laplacier/PCB-Business-Card-v2/KiCAD Files/PCB_Business_Card_v2.kicad_sch

## KiCad design KiCAD Files/PCB_Business_Card_v2.kicad_sch (2024-06-15)

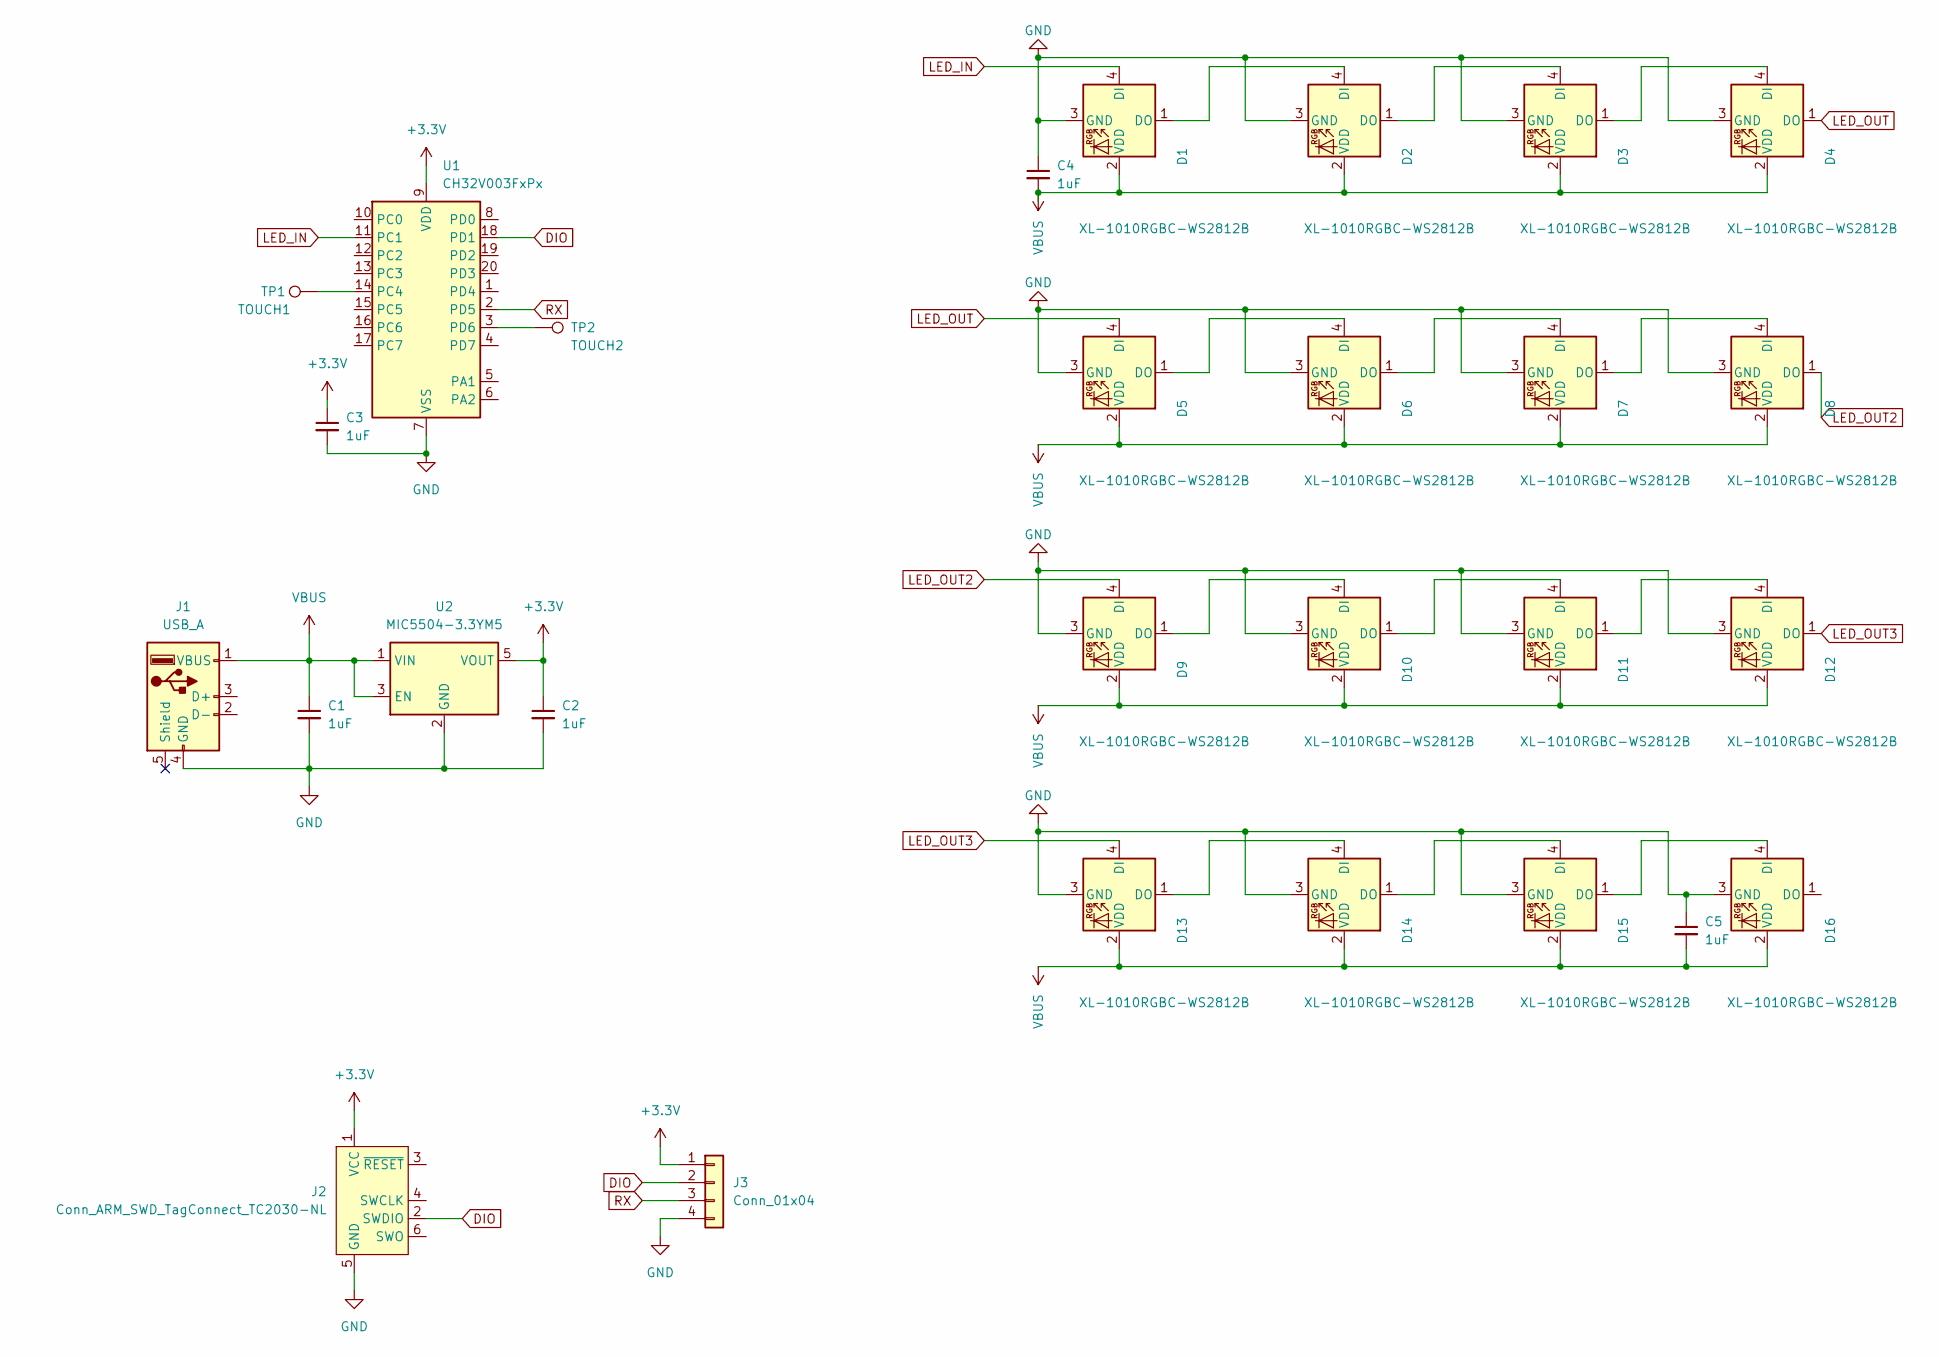
[picture p2: schematic PCB_Business_Card_v2.kicad_sch]

Parts:
C1, C2, C3, C4, C5: 1uF; C_0603_1608Metric_Pad1.08x0.95mm_HandSolder
D1, D2, D3, D4, D5, D6, D7, D8, D9, D10, D11, D12, D13, D14, D15, D16: XL-1010RGBC-WS2812B
J1: USB_A; USBA_RAW
J2: Conn_ARM_SWD_TagConnect_TC2030-NL; Tag-Connect_TC2030-IDC-NL_2x03_P1.27mm_Vertical
J3: Conn_01x04; PinHeader_1x04_P2.54mm_Vertical
TP1: TOUCH1; PAD_8x8
TP2: TOUCH2; PAD_8x8
U1: CH32V003FxPx; TSSOP-20_4.4x6.5mm_P0.65mm
U2: MIC5504-3.3YM5; SOT-23-5

Connections:
+3.3V: C2.1, C3.1, J2.1 (VCC), J3.1, U1.9 (VDD), U2.5 (VOUT)
DIO: J2.2 (SWDIO), J3.2, U1.18 (PD1)
GND: C1.2, C2.2, C3.2, C4.1, C5.1, D1.3 (GND), D2.3 (GND), D3.3 (GND), D4.3 (GND), D5.3 (GND), D6.3 (GND), D7.3 (GND), D8.3 (GND), D9.3 (GND), D10.3 (GND), D11.3 (GND), D12.3 (GND), D13.3 (GND), D14.3 (GND), D15.3 (GND), D16.3 (GND), J1.4 (GND), J2.5 (GND), J3.4, U1.7 (VSS), U2.2 (GND)
LED_IN: D1.4 (DI), U1.11 (PC1)
LED_OUT: D4.1 (DO), D5.4 (DI)
LED_OUT2: D8.1 (DO), D9.4 (DI)
LED_OUT3: D12.1 (DO), D13.4 (DI)
unnamed: D1.1 (DO), D2.4 (DI)
unnamed: D2.1 (DO), D3.4 (DI)
unnamed: D3.1 (DO), D4.4 (DI)
unnamed: D5.1 (DO), D6.4 (DI)
unnamed: D6.1 (DO), D7.4 (DI)
unnamed: D7.1 (DO), D8.4 (DI)
unnamed: D10.1 (DO), D11.4 (DI)
unnamed: D9.1 (DO), D10.4 (DI)
unnamed: D11.1 (DO), D12.4 (DI)
unnamed: D13.1 (DO), D14.4 (DI)
unnamed: D14.1 (DO), D15.4 (DI)
unnamed: D15.1 (DO), D16.4 (DI)
unnamed: TP1.1, U1.14 (PC4)
unnamed: TP2.1, U1.3 (PD6)
RX: J3.3, U1.2 (PD5)
VBUS: C1.1, C4.2, C5.2, D1.2 (VDD), D2.2 (VDD), D3.2 (VDD), D4.2 (VDD), D5.2 (VDD), D6.2 (VDD), D7.2 (VDD), D8.2 (VDD), D9.2 (VDD), D10.2 (VDD), D11.2 (VDD), D12.2 (VDD), D13.2 (VDD), D14.2 (VDD), D15.2 (VDD), D16.2 (VDD), J1.1 (VBUS), U2.1 (VIN), U2.3 (EN)
